tomasmcguinness/matter-esp32-mbus-adapter/tools/kamstrup-403-sim/mbusslave.h

/*
 * M-Bus slave link layer (EN 13757-2) for the Kamstrup MULTICAL 403 simulator.
 *
 * Structure derived from HWHardsoft/Arduino-MBUS-Meter, which in turn derives
 * from OpenEnergyMonitor's HeatpumpMonitor - GPLv3.
 *   https://github.com/HWHardsoft/Arduino-MBUS-Meter
 */
#ifndef MBUSSLAVE_H
#define MBUSSLAVE_H

#include <Arduino.h>

/* ---------------------------------------------------------------------------
 * Wiring - Raspberry Pi Pico (arduino-pico core)
 *
 *   GP0 (UART0 TX) --> M-Bus slave HAT modulator in
 *   GP1 (UART0 RX) <-- M-Bus slave HAT comparator out
 *   USB            <-> debug console @ 115200
 *
 * The HAT does the level conversion. On the wire, mark/idle is the high bus
 * voltage (~36 V) and a slave answers by modulating current, never by driving
 * voltage - see tools/pcb-test/README.md for the measured master-side numbers.
 * ------------------------------------------------------------------------- */
#define MBUS_TX_PIN 0
#define MBUS_RX_PIN 1

/* Neither RP2040 core gives Serial1 as a HardwareSerial, so the reference
 * sketch's `HardwareSerial *MBusSerial` will not compile on either. Plain
 * aliases sidestep the whole problem. */
#define MBUS_SERIAL  Serial1
#define DEBUG_SERIAL Serial

/* Two Arduino cores can target the Pico, and they differ on pin assignment:
 *
 *   earlephilhower's arduino-pico - Serial1 is a SerialUART whose TX and RX can
 *     be moved to another valid pin pair at runtime via setTX()/setRX().
 *
 *   Arduino's Mbed OS RP2040 core - Serial1 is an arduino::UART whose pins are
 *     fixed when it is constructed; there is no setTX/setRX. Its Serial1 is
 *     already on digital 0/1, which is GP0/GP1, so nothing needs moving and
 *     MBUS_TX_PIN/MBUS_RX_PIN below simply document the wiring.
 *
 * Both honour SERIAL_8E1, which is the part M-Bus actually depends on.
 * If you are on some third core whose Serial1 has no setTX/setRX, define
 * MBUS_SERIAL_PINS_FIXED=1 and wire the meter to that core's UART pins. */
#ifndef MBUS_SERIAL_PINS_FIXED
#if defined(ARDUINO_ARCH_MBED)
#define MBUS_SERIAL_PINS_FIXED 1
#else
#define MBUS_SERIAL_PINS_FIXED 0
#endif
#endif

/* Only arduino-pico lets the RX ring buffer be resized, and mbus_echo needs it:
 * the echo of a 63-byte telegram arrives while write() is still blocking, so
 * the default 32-byte buffer would overflow and fake a corrupted echo. */
#ifndef MBUS_SERIAL_HAS_FIFO_SIZE
#if defined(ARDUINO_ARCH_MBED)
#define MBUS_SERIAL_HAS_FIFO_SIZE 0
#else
#define MBUS_SERIAL_HAS_FIFO_SIZE 1
#endif
#endif

/* Link settings. The source of truth is the master:
 *   firmware/main/mbus.cpp:61-73 - 2400 baud, 8 data bits, EVEN parity, 1 stop
 *   firmware/main/mbus.h:9       - primary address 0x05
 * A mismatch here is the classic silent failure: the master simply times out
 * having received no bytes at all. */
#define MBUS_BAUD_RATE_DEFAULT 2400
#define MBUS_ADDRESS_DEFAULT   0x05
#define MBUS_SERIAL_CONFIG     SERIAL_8E1

#define MBUS_DATA_SIZE      255
#define MBUS_FRAME_MAX      266
#define MBUS_GAP_MS          50  /* inter-byte gap that abandons a frame.
                                  * One byte at 2400 8E1 takes ~4.6 ms. */
#define MBUS_ECHO_DRAIN_MS   15  /* let the HAT comparator settle after TX.
                                  * Must outlast the last character's echo,
                                  * which lands ~4.6 ms after the stop bit
                                  * leaves the UART, or mbus_echo below is
                                  * truncated by the drain rather than by the
                                  * bus. The master leaves 100 ms before its
                                  * next request, so this is free. */

#define DEBUG 1

/* --------------------------------------------------------------------------
 * C field (control): F = FCB, A = ACD, D = DFC
 *   SND_NKE  init slave           0100 0000  0x40        short frame
 *   SND_UD   send user data       01F1 0011  0x53 / 0x73 long frame
 *   REQ_UD2  request class 2 data 01F1 1011  0x5B / 0x7B short frame
 *   REQ_UD1  request class 1 data 01F1 1010  0x5A / 0x7A short frame
 *   RSP_UD   data from slave      00AD 1000  0x08 ...    long frame
 * Masking with FCB_BIT_MASK ignores the toggling FCB bit. This master never
 * toggles it (it re-sends SND_NKE before every poll instead), but a real
 * master will.
 * ------------------------------------------------------------------------ */
#define MBUS_SND_NKE 0x40
#define MBUS_SND_UD  0x53
#define MBUS_REQ_UD1 0x5A
#define MBUS_REQ_UD2 0x5B
#define MBUS_RSP_UD  0x08
#define FCB_BIT_MASK 0xDF

#define MBUS_FRAME_SHORT_START 0x10
#define MBUS_FRAME_LONG_START  0x68
#define MBUS_FRAME_STOP        0x16
#define MBUS_ACK               0xE5

/* CI field */
#define MBUS_CI_DATA_SEND  0x51 /* master -> slave, data send            */
#define MBUS_CI_SELECT     0x52 /* master -> slave, selection of slaves  */
#define MBUS_CI_RSP_LONG   0x72 /* slave -> master, variable data, 12-byte header */

/* Broadcast addresses: 0xFD (no reply) and 0xFE (reply). 0 is unconfigured. */
#define MBUS_ADDR_BROADCAST_NOREPLY 0xFD
#define MBUS_ADDR_BROADCAST_REPLY   0xFE

/* --------------------------------------------------------------------------
 * Kamstrup MULTICAL 403 identity, as it appears in the 12-byte fixed header.
 * ------------------------------------------------------------------------ */
#define KAM_MANUFACTURER 0x2C2D     /* 'K','A','M' packed per EN 13757-3;
                                     * transmitted little-endian as 2D 2C   */
#define KAM_VERSION      0x34       /* generation/version byte              */
#define KAM_MEDIUM       0x04       /* heat, volume measured at return      */
#define KAM_STATUS       0x00       /* no alarm, no error                   */
#define KAM_SERIAL       12345678UL /* 8 digits, encoded BCD LSB first      */

/* --------------------------------------------------------------------------
 * API
 * ------------------------------------------------------------------------ */

/* Bench aid. When >= 0, every "don't care" byte of the telegram - the status
 * and signature bytes of the fixed header, and all data-record values - is
 * replaced by this fill byte. Structure, record count and frame length are
 * untouched, so only the telegram's *bit pattern* changes. -1 = real values.
 *
 * Written to test whether a master was failing on long runs of space bits. An
 * earlier note here concluded it was not, on the strength of 0x55 fill
 * corrupting at the same byte index as real zero-heavy values. That was wrong:
 * the telegram was also truncating at the time for a second reason, and the
 * truncation masked the pattern effect. Measured again against the ESP32-C6
 * master, with the frame short enough to arrive whole, two variables separate
 * cleanly:
 *
 *   POSITION. Every character below byte index ~31 - about 140 ms into a
 *   continuous transmission at 2400 baud - survives whatever it contains. The
 *   index reproduced to the byte across 33- and 45-byte telegrams.
 *
 *   SPACE CONTENT. At that index a character carrying 8 space bit-times out of
 *   11 corrupts, and one carrying 6 does not. For 8E1 the count is
 *   10 - popcount - (popcount & 1), so the rule is popcount <= 2. Observed on
 *   the checksum byte as the access number walked it: 04 -> CC, 05 -> C5,
 *   06 -> C6 (popcount 1, 2, 2) and 07 -> 07 clean (popcount 3). Every flip is
 *   0 -> 1 and sits at the trailing end of the character - the space current
 *   sagging back to mark, not a framing slip.
 *
 * Longest run is NOT the discriminator: 0x04 and 0x07 share a 5-bit run and
 * only 0x04 fails. See mbus_tx_gap_us for the recovery side of the effect.
 *
 * A 0x11 fill (8 space bits, 73% of the character sinking current, against
 * 0x55's 6 bits and 55%) then sharpened it:
 *
 *   The state that decides failure is built by the PRECEDING traffic. Sent
 *   index 19 is the byte 0x04 in both fills, at the same position in the
 *   telegram. Under 0x55 it decodes; under 0x11 it is the first byte to
 *   corrupt. Nothing about the character or its position changed - only what
 *   ran before it.
 *
 *   Accumulated charge is NOT the invariant either. 0x11 first fails after 128
 *   space bit-times of transmission, 0x55 survives to 200. A fixed charge
 *   budget would have put both at the same number, so this is a droop with a
 *   recovery path - recent duty matters more than the total. Fitting a leaky
 *   integrator to the four failures so far only works at tau ~ 100 bit-times
 *   (~42 ms) and separates pass from fail by 2%, which is not a number worth
 *   trusting. It needs a duty sweep: 0xFF 18%, 0x3F 36%, 0x55 55%, 0x11 73%,
 *   0x00 91%, recording the first corrupt index for each. 0x03 against 0x11 is
 *   the control - same 73% duty, runs of 7 and 4 - and separates duty from run
 *   structure.
 *
 *   Corruption costs whole CHARACTERS, not just bits. Once a space sags to
 *   mark the receiver loses character framing and re-triggers on a data bit as
 *   a false start bit. Reconstructing one 0x11 telegram bit by bit, all 39
 *   received bytes sat at monotonically advancing offsets in the transmitted
 *   stream, but 6 of them were read at phases of +2 to +9 bits and 24 sent
 *   characters produced no received character at all.
 *
 *   So "Frame stalled: N of M bytes" from the master does NOT mean the slave
 *   stopped talking. In that telegram the trailing 0x16 was not the stop byte;
 *   it was sent index 55 read 7 bits out of phase, and the slave transmitted
 *   all 63 characters. Read a short frame as lost framing until the bit-level
 *   reconstruction says otherwise.
 *
 * Not the master's UART driver: the FRAM_ERR and PARITY_ERR paths in
 * esp_driver_uart (checked against ESP-IDF v5.5.4, the version firmware/ builds
 * against) do not reset the RX FIFO - only FIFO overflow and the RS485 modes
 * do - so a bad character does not take buffered good ones with it.
 *
 * To bisect the cliff, fill with a low-popcount byte: every payload character
 * is then vulnerable rather than just the DIF/VIF bytes, and the first corrupt
 * index in the master's hexdump reads the cliff position off directly.
 *
 *   0x55   6 space bits of 11, longest run  2  - healthy, the default probe
 *   0x11   8 of 11, longest run  4             - vulnerable, short runs
 *   0x03   8 of 11, longest run  7             - vulnerable, one long run
 *   0x00  10 of 11, longest run 10             - worst case
 *
 * 0x11 against 0x03 is the pair worth running: identical charge, very
 * different run structure. Same failure index means charge alone decides it;
 * 0x03 failing earlier means run length matters too.
 *
 * Still useful for reading dumps: a phase-slipped 0x55 stream can only decode
 * as 55/95/a5/a9/aa, so anything else in a 0x55 frame is real bit distortion.
 *
 * Set from the serial console: 'f' then two hex digits, 'p' for 0x55, 'r' for
 * real values. */
extern int16_t mbus_fill_byte;

/* Idle mark time inserted after every transmitted byte, in MICROSECONDS.
 *
 * 0 = characters back-to-back, which is what a real MULTICAL 403 does and what
 * EN 13757-2 expects (the gap between characters of one telegram is capped at
 * around 11 bit times, ~4.6 ms at 2400 baud).
 *
 * This is the knob that matters on a marginal bus. Measured on the Rev G
 * board: at 0 the telegram corrupts from byte ~17 onward, about 80 ms into the
 * transmission, whatever the payload. At 2000 us it decodes cleanly all the
 * way through - and the frame then takes 415 ms rather than 289 ms, so it is
 * not elapsed time that matters but the proportion of it spent sinking space
 * current. Roughly 70% transmit duty is sustainable; 100% is not.
 *
 * That asymmetry - ~80 ms to fail, ~2 ms of idle per character to stay healthy
 * - is what a bus-powered slave running at the edge of its power budget looks
 * like: a reservoir that drains slowly under continuous modulation and refills
 * quickly once the line goes back to mark.
 *
 * HWHardsoft/Arduino-MBUS-Meter - the sketch this one is modelled on - delays
 * 10 ms after every byte at 2400 baud (transmit_delay_time()), which is why it
 * appeared to work on hardware that a faithful simulator breaks.
 *
 * Keep this at 0 for honest testing. Raise it to reproduce the reference
 * sketch, or to measure how much idle a marginal setup needs - the smallest
 * gap that decodes cleanly, plus the 417 us stop bit, is that number. */
extern uint16_t mbus_tx_gap_us;

/* The slave's own last transmission, as it came back through the HAT's
 * comparator. The HAT loops it back - mbus_tx_done() has always had to drain it
 * so the next mbus_get_response() does not parse our own reply as a master
 * command - and that loopback is a free measurement point.
 *
 * It splits the bus in half without instruments. The path here is
 *   UART TX -> HAT modulator -> bus -> HAT comparator
 * where what the master decodes adds
 *   -> DYBKRADIO comparator -> ESP32 UART.
 * So a corrupted echo puts the fault at the slave end or on the bus itself,
 * and a clean echo against a corrupted master copy puts it at the master end.
 * A zero-length echo just means this HAT does not loop back, and the test is
 * unavailable rather than passed.
 *
 * Compare against what was transmitted with mbus_report_echo() in the sketch.
 * Empty until the first transmission. */
extern uint8_t mbus_echo[MBUS_FRAME_MAX];
extern size_t mbus_echo_len;

/* Encode KAM_SERIAL as the four BCD identification bytes, LSB first. */
void mbus_id_bytes(uint8_t out[4]);

/* Read one frame from the bus.
 *   >0  frame length in bytes, checksum verified, stored in pdata
 *    0  nothing waiting - the caller should get on with other work
 *   -1  malformed frame (bad length, checksum, or stop byte) */
int mbus_get_response(uint8_t *pdata, size_t cap);

/* Build a RSP_UD long frame around `records`, returning its length.
 * Increments the access number. Does not transmit. */
int mbus_build_frame(uint8_t c_field, uint8_t address,
                     const uint8_t *records, uint8_t records_len,
                     uint8_t *frame, size_t cap);

void mbus_transmit(const uint8_t *frame, size_t len);
void mbus_send_ack(void);

#endif /* MBUSSLAVE_H */
